UCHIC/CIWS-WM-Node/Firmware/Computational_Firmware/powerSleep.h

#ifndef POWERSLEEP_H
#define POWERSLEEP_H

#include <avr/sleep.h>
#include <avr/power.h>

//void enterSleep();
void disableUnneededPeripherals();
void twiPowerUp();
void twiPowerDown();
void serialPowerUp();
void serialPowerDown();
void spiPowerUp();
void spiPowerDown();

#endif
